f0x3s/Olalekan-Jeyifous-HL-Fluvial-Taxonomies-wall-mounts-WAC/3d-files/isolated-mount-export/B_10_LO.stl

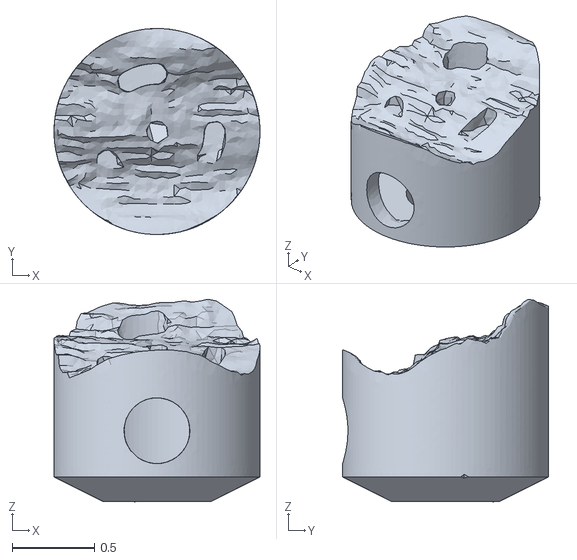
[picture p20: CAD file, 2026-07-31]
3d-files/isolated-mount-export/B_10_LO.stl
1.25 x 1.25 x 1.23
