f0x3s/Olalekan-Jeyifous-HL-Fluvial-Taxonomies-wall-mounts-WAC/ready-for-print/printed/I_19_for-print.stl

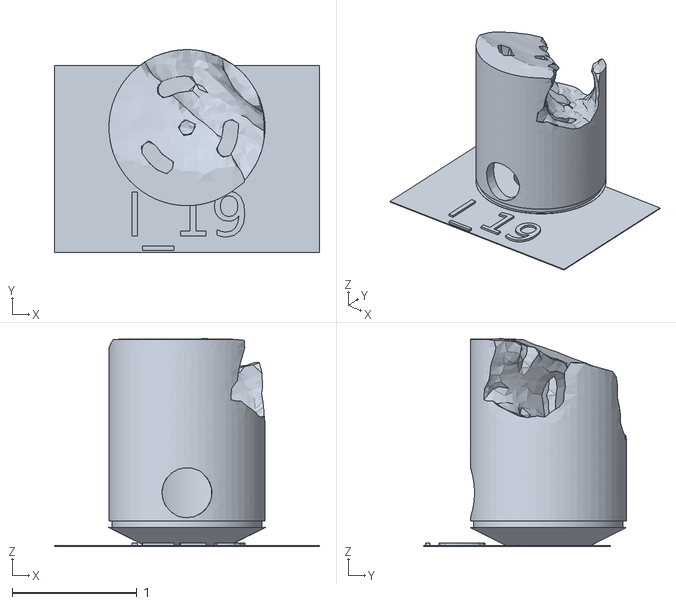
[picture p21: CAD file, 2026-07-31]
ready-for-print/printed/I_19_for-print.stl
2.12 x 1.63 x 1.67
