f0x3s/Olalekan-Jeyifous-HL-Fluvial-Taxonomies-wall-mounts-WAC/3d-files/isolated-mount-export/I_21.stl

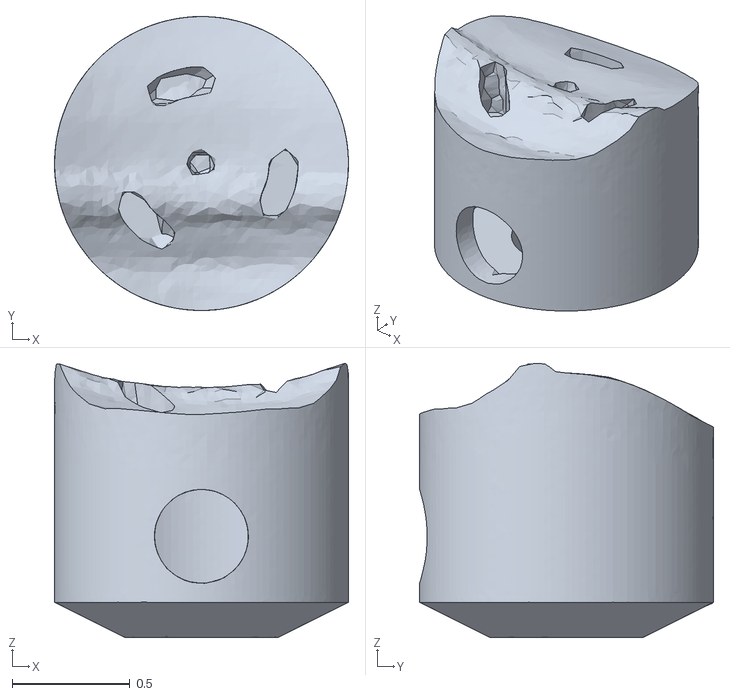
[picture p22: CAD file, 2026-07-31]
3d-files/isolated-mount-export/I_21.stl
1.25 x 1.25 x 1.17
